j54n1n/usbprog/board/selfmade_v3/ReadMe.txt

...noch ein Layout...

Moin!

Anbei ein weiteres Layout zum selber Ätzen. Dabei wurde der Schaltplan 
des originalen USBprog (Version 3.1) 1:1 übernommen und lediglich 
wenige Bauteilgrößen aus Routinggründen geändert. Das Layout ist 
komplett einseitig mit nur fünf Lötbrücken. Drei der Lötbrücken können 
theoretisch durch 0Ohm-Widerstände mit 1206er Baugröße ersetzt werden.
Hierauf habe ich allerdings verzichtet, da es sich bei den Brücken um 
die Versorgungsspannung handelt.
Die Abmessung der Platine ist mit 80mm x 37mm handlich geblieben.

Die abgeänderten Bauteilgrößen sind:
Name        Wert     Änderung
-----------+--------+-------------------------------
J1          -        Mini-USB-B statt Standard-USB-B
LED1,LED2   rt, gn   3mm-DIL statt 0603SMD
R8-15       100      1206 statt 0603
R7          10k      1206 statt 0603

Viel Spass beim Nachbauen!

MfG,
Thomas
<etechnik@gmx.info>
