j54n1n/usbprog/usbprogLCD/lcdhype/readme.txt

LCDHype Treiber für usbprog_lcd
===============================
(getestet mit LCDHype 0.42)

1. Treiber installieren
=======================
Komplettes Verzeichnis "usbprog" (inkl. Verzeichnisname) kopieren nach
C:\Programme\LCDHype\controller
In LCDHype unter Einstellungen => LCD-Einstellungen auswählen:
USBprog

2. Plugin für WinAmp installieren
=================================
Plugin für WinAmp (V2.xx) installieren (getestet mit WinAmp 2.73)
Alle Dateien aus dem Verzeichnis "winamp" kopieren nach
C:\Programme\Winamp\Plugins

3. Beispielskript
=================
Beispielskript zur Ausgabe von Titel/Interpret und Spektrumanalyzer aus WinAmp:
Datei "usblcd.sd" kopieren nach
C:\Programme\LCDHype\scripts
In LCDHype unter LCD-Anzeige dieses Skript laden und mit dem Go-Button starten.
