j54n1n/usbprog/board/hvpp.png

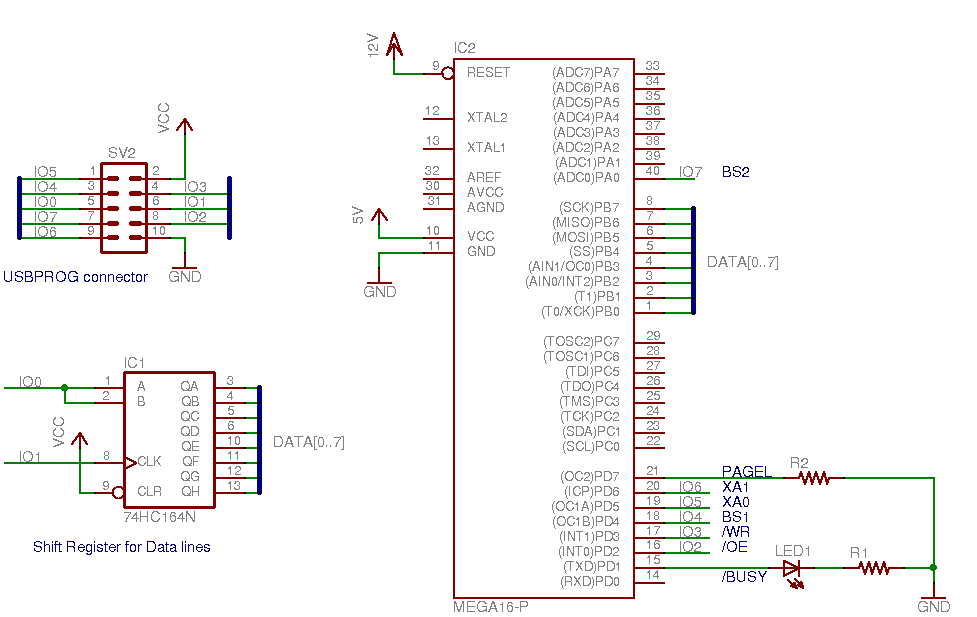
board/hvpp.png
