j54n1n/usbprog/board/levelshifter/screenshot.png

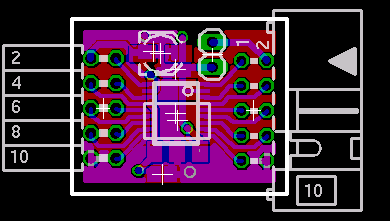
board/levelshifter/screenshot.png
