j54n1n/usbprog/board/selfmade_v3/bottom.jpg

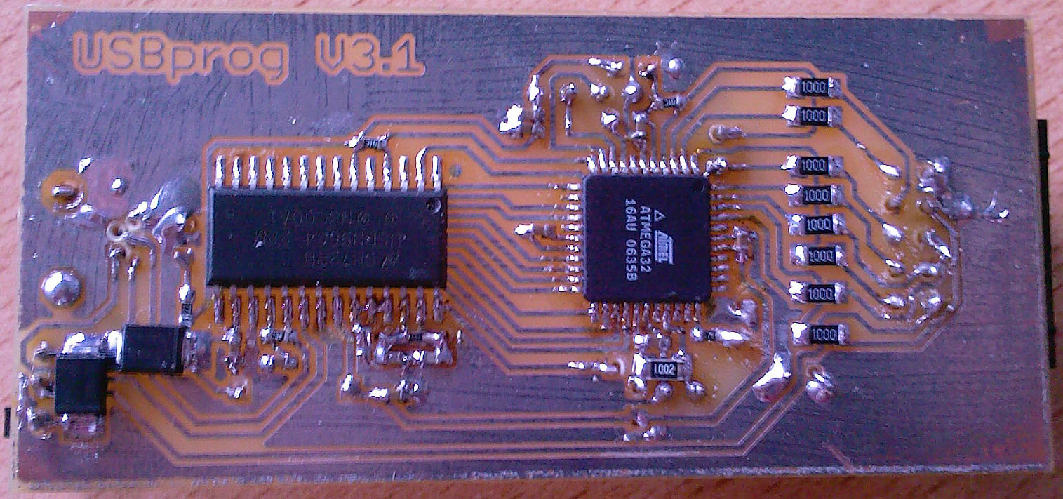
board/selfmade_v3/bottom.jpg
