j54n1n/usbprog/board/selfmade_v3/top.jpg

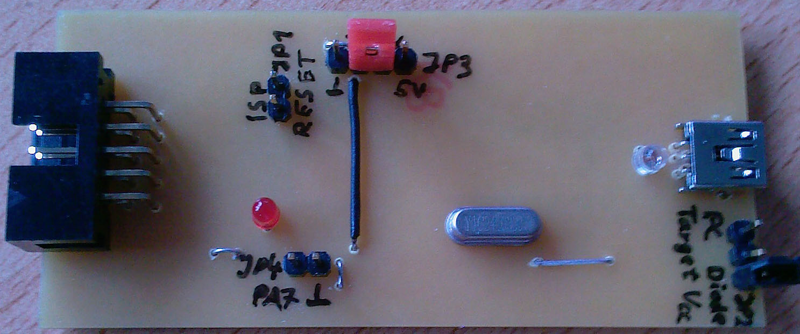
board/selfmade_v3/top.jpg
