j54n1n/usbprog/misc/selfmade_usbprog/BC5G3316.jpg

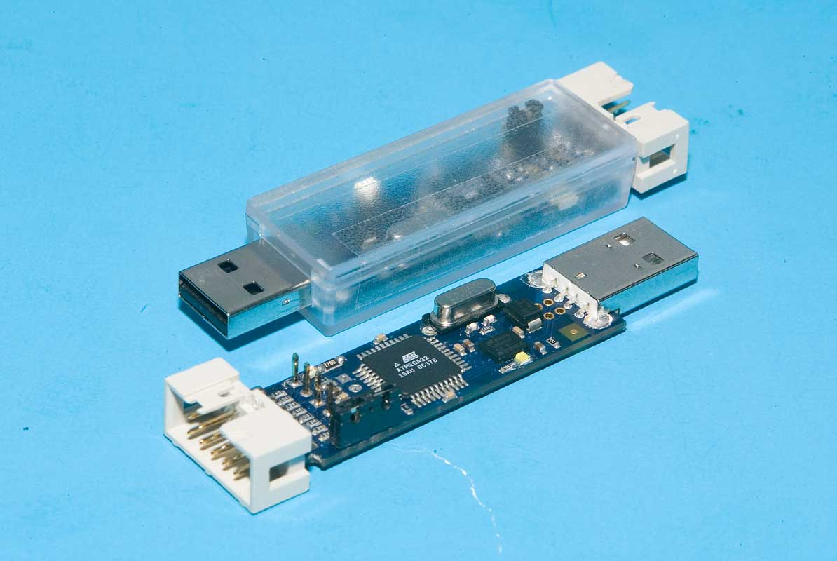
misc/selfmade_usbprog/BC5G3316.jpg
