j54n1n/usbprog/misc/selfmade_usbprog/P1010025.JPG

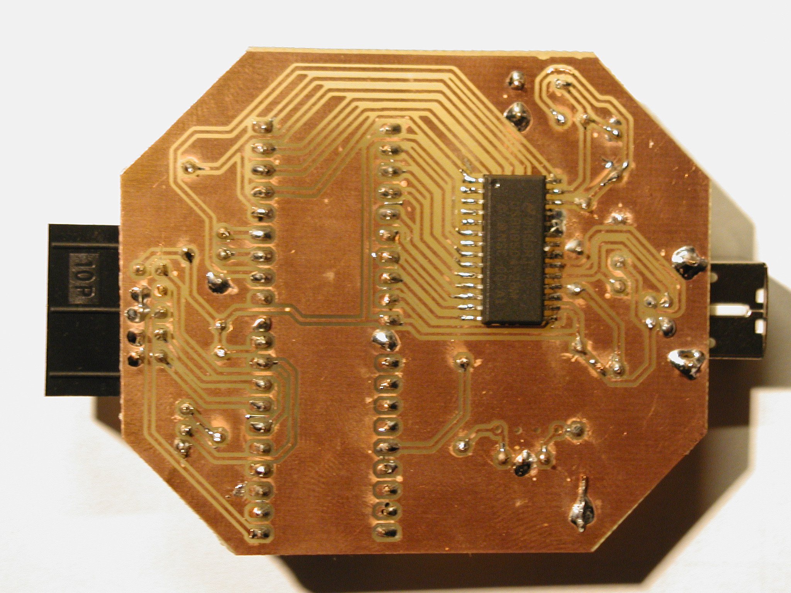
misc/selfmade_usbprog/P1010025.JPG
