j54n1n/usbprog/misc/selfmade_usbprog/P1010026.JPG

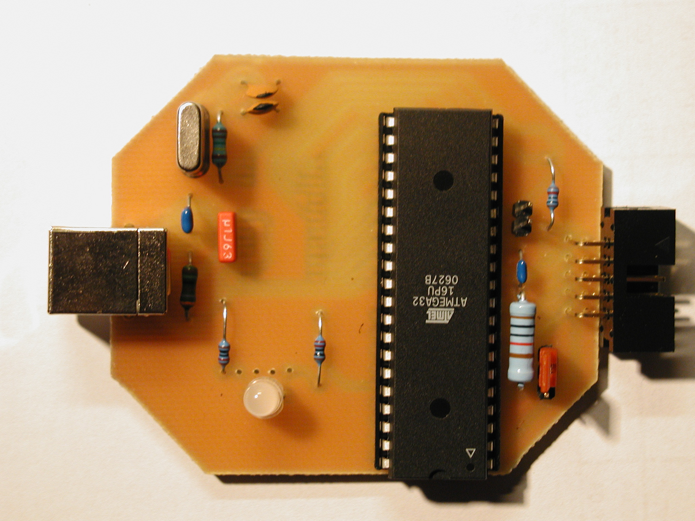
misc/selfmade_usbprog/P1010026.JPG
