j54n1n/usbprog/misc/selfmade_usbprog/UsbProgSharp-copper.jpg

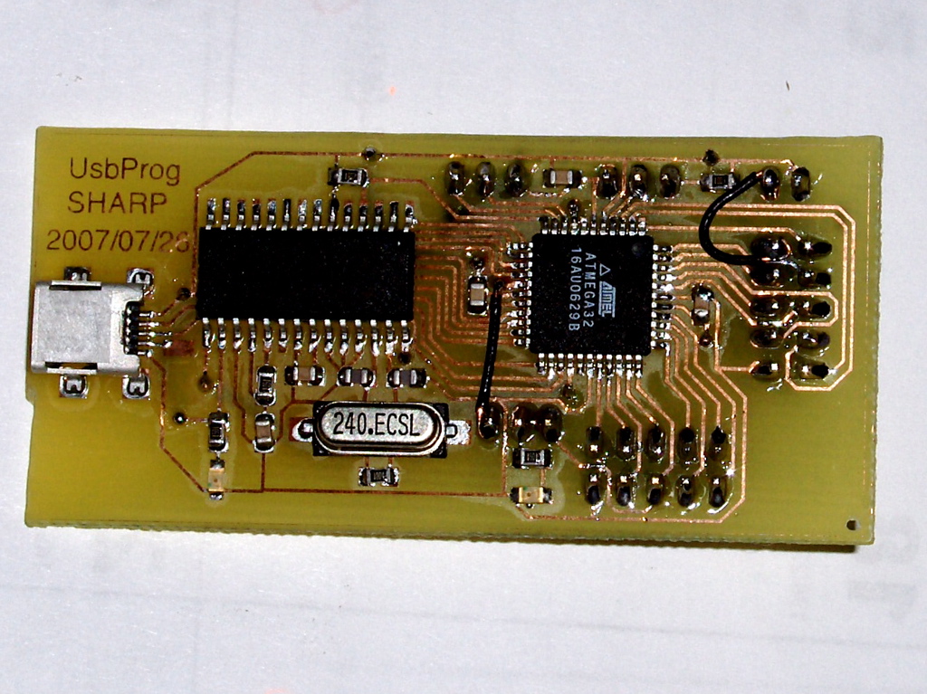
misc/selfmade_usbprog/UsbProgSharp-copper.jpg
