j54n1n/usbprog/usbprogCAN/board/usbprogCAN.png

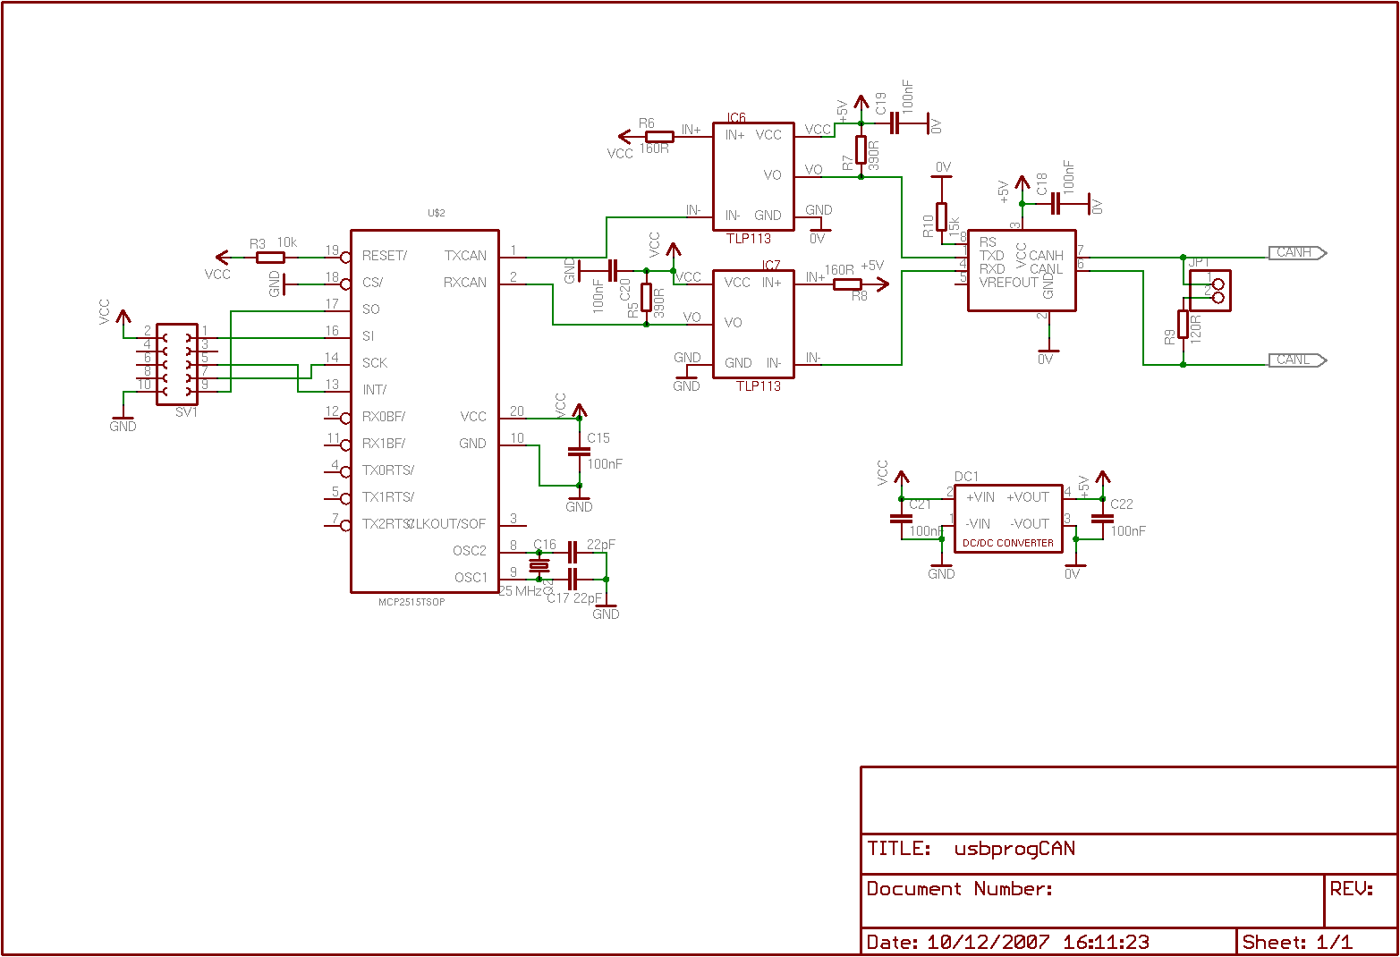
usbprogCAN/board/usbprogCAN.png
