j54n1n/usbprog/usbprogJTAG/openwince/website/iPAQ-3600/images/4.jpg

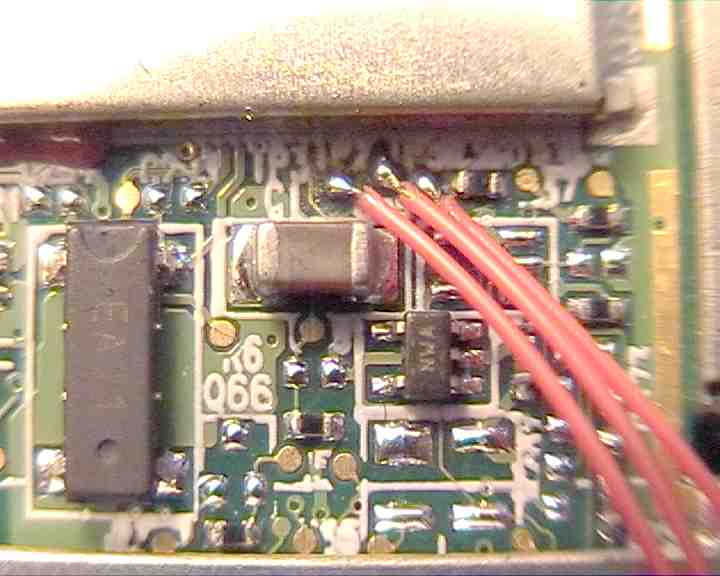
usbprogJTAG/openwince/website/iPAQ-3600/images/4.jpg
