j54n1n/usbprog/usbprogJTAG/openwince/website/iPAQ-3600/images/7.jpg

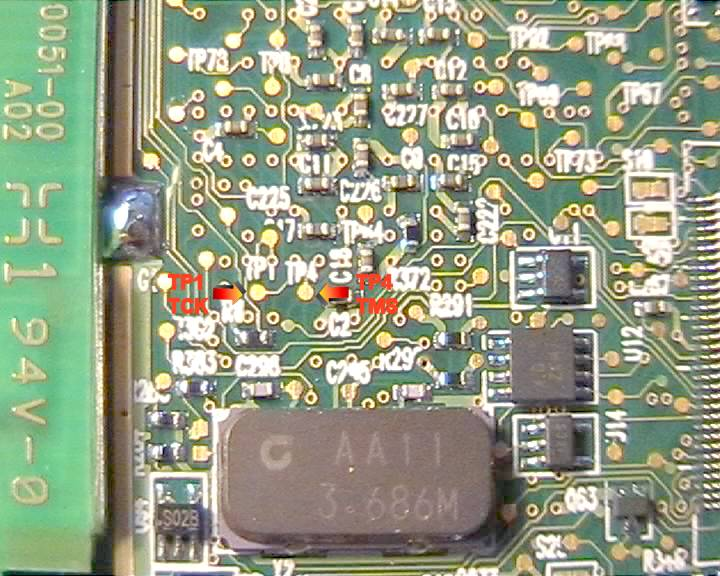
usbprogJTAG/openwince/website/iPAQ-3600/images/7.jpg
