j54n1n/usbprog/usbprogJTAG/openwince/website/iPAQ-3600/images/12.jpg

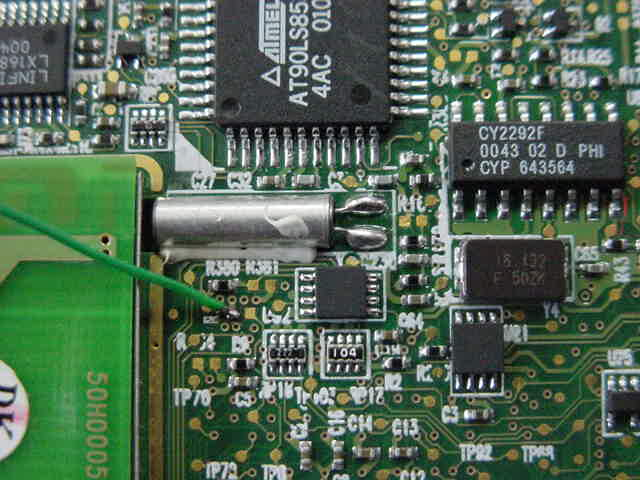
usbprogJTAG/openwince/website/iPAQ-3600/images/12.jpg
