j54n1n/usbprog/usbprogJTAG/openwince/website/iPAQ-3600/images/A.jpg

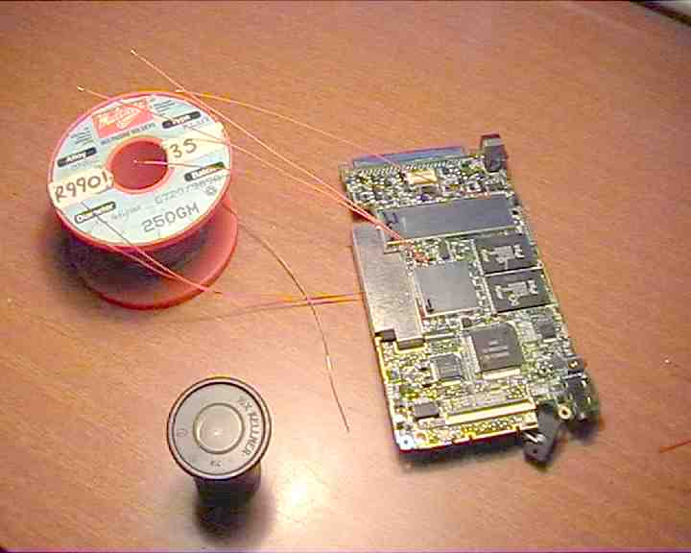
usbprogJTAG/openwince/website/iPAQ-3600/images/A.jpg
