j54n1n/usbprog/usbprogJTAG/openwince/website/iPAQ-3600/images/B.jpg

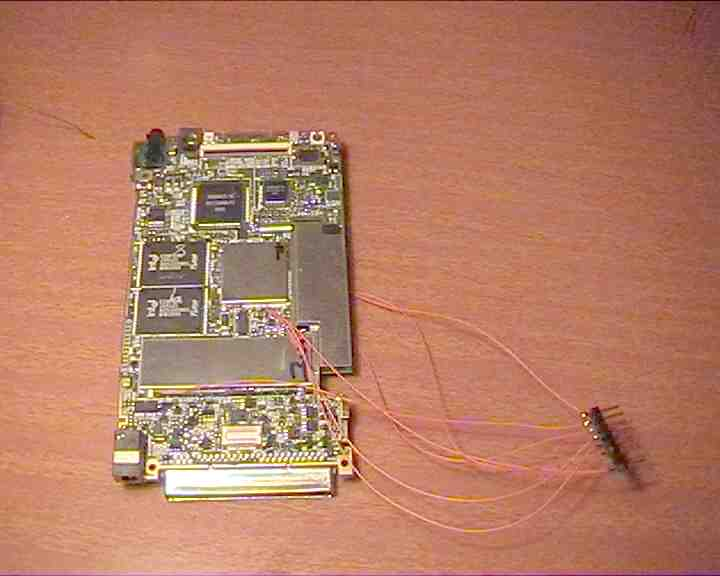
usbprogJTAG/openwince/website/iPAQ-3600/images/B.jpg
