j54n1n/usbprog/usbprogLCD/images/lcd.jpg

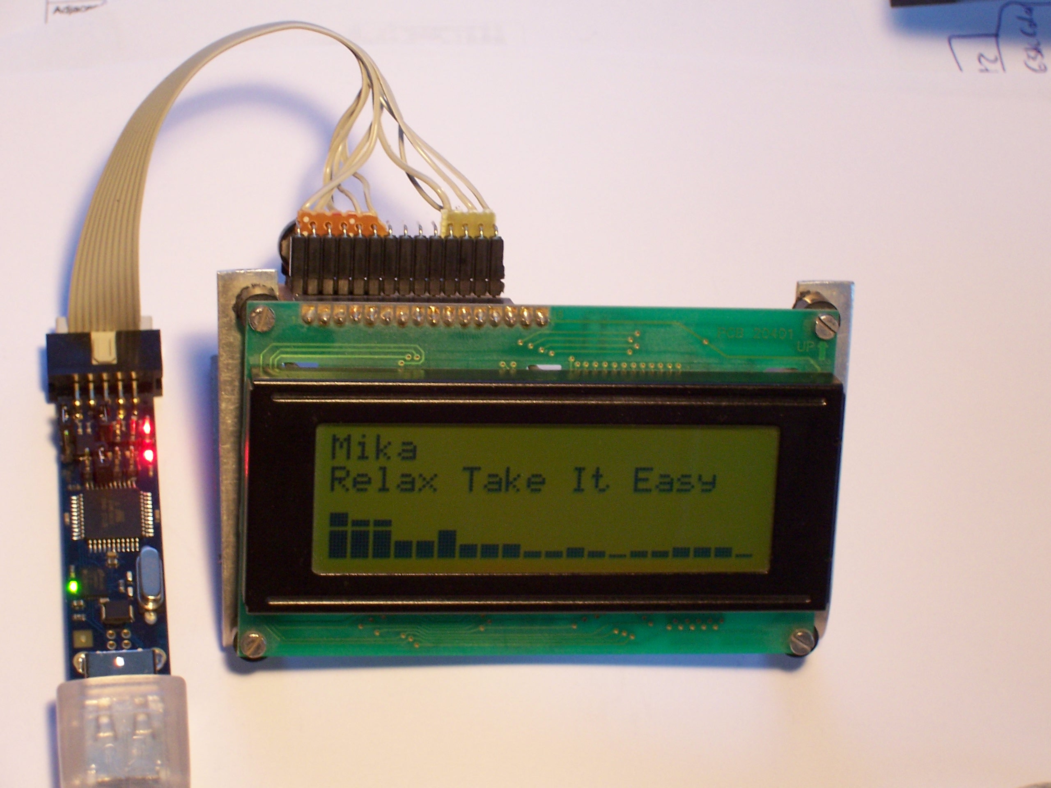
usbprogLCD/images/lcd.jpg
