j54n1n/usbprog/usbprogPIC/levelshifter/circuit.png

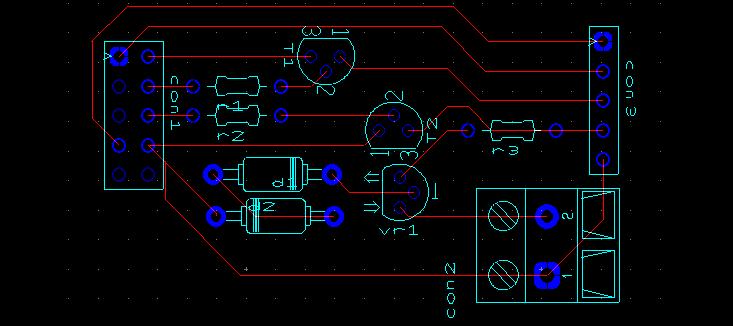
usbprogPIC/levelshifter/circuit.png
