j54n1n/usbprog/usbprogJTAG/openwince-include-0.4.2/arm/pxa2x0/gpio.h

/*
 * $Id: gpio.h,v 1.14 2005/09/29 08:51:07 telka Exp $
 *
 * XScale PXA26x/PXA255/PXA250/PXA210 GPIO Registers
 * Copyright (C) 2002, 2003 ETC s.r.o.
 * All rights reserved.
 *
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
 * Written by Marcel Telka <marcel@telka.sk>, 2002, 2003.
 *
 * Documentation:
 * [1] Intel Corporation, "Intel PXA250 and PXA210 Application Processors
 *     Developer's Manual", February 2002, Order Number: 278522-001
 * [2] Intel Corporation, "Intel PXA26x Processor Family Developer's Manual",
 *     March 2003, Order Number: 278638-002
 * [3] Intel Corporation, "Intel PXA255 Processor Developer's Manual"
 *     March 2003, Order Number: 278693-001
 *
 */

#ifndef	PXA2X0_GPIO_H
#define	PXA2X0_GPIO_H

#include <openwince.h>

#if LANGUAGE == C
#include <stdint.h>
#endif

#if defined(PXA2X0_NOPXA250) && !defined(PXA2X0_NOPXA255)
#define PXA2X0_NOPXA255
#endif

#if defined(PXA2X0_NOPXA255) && !defined(PXA2X0_NOPXA260)
#define PXA2X0_NOPXA260
#endif

/* GPIO Registers */

#define	GPIO_BASE	0x40E00000

#if LANGUAGE == C
typedef volatile struct GPIO_registers {
	uint32_t gplr0;
	uint32_t gplr1;
	uint32_t gplr2;
	uint32_t gpdr0;
	uint32_t gpdr1;
	uint32_t gpdr2;
	uint32_t gpsr0;
	uint32_t gpsr1;
	uint32_t gpsr2;
	uint32_t gpcr0;
	uint32_t gpcr1;
	uint32_t gpcr2;
	uint32_t grer0;
	uint32_t grer1;
	uint32_t grer2;
	uint32_t gfer0;
	uint32_t gfer1;
	uint32_t gfer2;
	uint32_t gedr0;
	uint32_t gedr1;
	uint32_t gedr2;
	uint32_t gafr0_l;
	uint32_t gafr0_u;
	uint32_t gafr1_l;
	uint32_t gafr1_u;
	uint32_t gafr2_l;
	uint32_t gafr2_u;
} GPIO_registers_t;

#ifdef PXA2X0_UNMAPPED
#define	GPIO_pointer	((GPIO_registers_t*) GPIO_BASE)
#endif

#define	GPLR0		GPIO_pointer->gplr0
#define	GPLR1		GPIO_pointer->gplr1
#define	GPLR2		GPIO_pointer->gplr2
#define	GPDR0		GPIO_pointer->gpdr0
#define	GPDR1		GPIO_pointer->gpdr1
#define	GPDR2		GPIO_pointer->gpdr2
#define	GPSR0		GPIO_pointer->gpsr0
#define	GPSR1		GPIO_pointer->gpsr1
#define	GPSR2		GPIO_pointer->gpsr2
#define	GPCR0		GPIO_pointer->gpcr0
#define	GPCR1		GPIO_pointer->gpcr1
#define	GPCR2		GPIO_pointer->gpcr2
#define	GRER0		GPIO_pointer->grer0
#define	GRER1		GPIO_pointer->grer1
#define	GRER2		GPIO_pointer->grer2
#define	GFER0		GPIO_pointer->gfer0
#define	GFER1		GPIO_pointer->gfer1
#define	GFER2		GPIO_pointer->gfer2
#define	GEDR0		GPIO_pointer->gedr0
#define	GEDR1		GPIO_pointer->gedr1
#define	GEDR2		GPIO_pointer->gedr2
#define	GAFR0_L		GPIO_pointer->gafr0_l
#define	GAFR0_U		GPIO_pointer->gafr0_u
#define	GAFR1_L		GPIO_pointer->gafr1_l
#define	GAFR1_U		GPIO_pointer->gafr1_u
#define	GAFR2_L		GPIO_pointer->gafr2_l
#define	GAFR2_U		GPIO_pointer->gafr2_u
#endif /* LANGUAGE == C */

#define	GPLR0_OFFSET	0x00
#define	GPLR1_OFFSET	0x04
#define	GPLR2_OFFSET	0x08
#define	GPDR0_OFFSET	0x0C
#define	GPDR1_OFFSET	0x10
#define	GPDR2_OFFSET	0x14
#define	GPSR0_OFFSET	0x18
#define	GPSR1_OFFSET	0x1C
#define	GPSR2_OFFSET	0x20
#define	GPCR0_OFFSET	0x24
#define	GPCR1_OFFSET	0x28
#define	GPCR2_OFFSET	0x2C
#define	GRER0_OFFSET	0x30
#define	GRER1_OFFSET	0x34
#define	GRER2_OFFSET	0x38
#define	GFER0_OFFSET	0x3C
#define	GFER1_OFFSET	0x40
#define	GFER2_OFFSET	0x44
#define	GEDR0_OFFSET	0x48
#define	GEDR1_OFFSET	0x4C
#define	GEDR2_OFFSET	0x50
#define	GAFR0_L_OFFSET	0x54
#define	GAFR0_U_OFFSET	0x58
#define	GAFR1_L_OFFSET	0x5C
#define	GAFR1_U_OFFSET	0x60
#define	GAFR2_L_OFFSET	0x64
#define	GAFR2_U_OFFSET	0x68

/* GPIO bits - see Table 2-11 in [1] */

#define	GPIO0_GP0	bit(0)
#define	GPIO0_GP1	bit(1)
#if !defined(PXA2X0_NOPXA250)
#define	GPIO0_GP2	bit(2)
#define	GPIO0_GP3	bit(3)
#define	GPIO0_GP4	bit(4)
#define	GPIO0_GP5	bit(5)
#define	GPIO0_GP6	bit(6)
#define	GPIO0_GP7	bit(7)
#define	GPIO0_GP8	bit(8)
#define	GPIO0_GP9	bit(9)
#define	GPIO0_GP10	bit(10)
#define	GPIO0_GP11	bit(11)
#define	GPIO0_GP12	bit(12)
#define	GPIO0_GP13	bit(13)
#define	GPIO0_GP14	bit(14)
#endif /* PXA250 and above only */
#define	GPIO0_GP15	bit(15)
#define	GPIO0_GP16	bit(16)
#define	GPIO0_GP17	bit(17)
#define	GPIO0_GP18	bit(18)
#if !defined(PXA2X0_NOPXA250)
#define	GPIO0_GP19	bit(19)
#define	GPIO0_GP20	bit(20)
#define	GPIO0_GP21	bit(21)
#define	GPIO0_GP22	bit(22)
#endif /* PXA250 and above only */
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
#define	GAFR2_L_AF76(x)	(((x) & ALT_FN_MASK) << 24)
#define	GAFR2_L_AF77(x)	(((x) & ALT_FN_MASK) << 26)
#define	GAFR2_L_AF78(x)	(((x) & ALT_FN_MASK) << 28)
#define	GAFR2_L_AF79(x)	(((x) & ALT_FN_MASK) << 30)

/* GAFR2_U bits - see Table 4-29 in [1], Table 4-29 in [2], Table 4-29 in [3] */

#define	GAFR2_U_AF80(x)	((x) & ALT_FN_MASK)
#if !defined(PXA2X0_NOPXA255)
#define	GAFR2_U_AF81(x)	(((x) & ALT_FN_MASK) << 2)
#define	GAFR2_U_AF82(x)	(((x) & ALT_FN_MASK) << 4)
#define	GAFR2_U_AF83(x)	(((x) & ALT_FN_MASK) << 6)
#define	GAFR2_U_AF84(x)	(((x) & ALT_FN_MASK) << 8)
#endif /* PXA255 and above only */
#if !defined(PXA2X0_NOPXA260)
#define	GAFR2_U_AF85(x)	(((x) & ALT_FN_MASK) << 10)
#define	GAFR2_U_AF86(x)	(((x) & ALT_FN_MASK) << 12)
#define	GAFR2_U_AF87(x)	(((x) & ALT_FN_MASK) << 14)
#define	GAFR2_U_AF88(x)	(((x) & ALT_FN_MASK) << 16)
#define	GAFR2_U_AF89(x)	(((x) & ALT_FN_MASK) << 18)
#endif /* PXA260 and above only */

#endif /* PXA2X0_GPIO_H */
