j54n1n/usbprog/misc/avarice_corner/avarice/src/main.cc

/*
 *	avarice - The "avarice" program.
 *	Copyright (C) 2001 Scott Finneran
 *	Copyright (C) 2002, 2003, 2004 Intel Corporation
 *	Copyright (C) 2005,2006 Joerg Wunsch
 *
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
 *
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
 * This file contains the main() & support for avrjtagd.
 *
 * $Id: main.cc,v 1.38 2006/10/28 20:17:31 joerg_wunsch Exp $
 */


#include <ctype.h>
#include <stdio.h>
#include <stdlib.h>
#include <string.h>
#include <sys/types.h>
#include <sys/socket.h>
#include <termios.h>
#include <arpa/inet.h>
#include <netdb.h>
#include <netinet/in.h>
#include <unistd.h>
#include <netinet/tcp.h>
#include <fcntl.h>

#include "avarice.h"
#include "remote.h"
#include "jtag.h"
#include "jtag1.h"
#include "jtag2.h"
#include "gnu_getopt.h"

bool ignoreInterrupts;

static int makeSocket(struct sockaddr_in *name, unsigned short int port)
{
    int sock;
    int tmp;
    struct protoent *protoent;

    sock = socket(PF_INET, SOCK_STREAM, 0);
    gdbCheck(sock);

    // Allow rapid reuse of this port.
    tmp = 1;
    gdbCheck(setsockopt(sock, SOL_SOCKET, SO_REUSEADDR, (char *)&tmp, sizeof(tmp)));

    // Enable TCP keep alive process.
    tmp = 1;
    gdbCheck(setsockopt(sock, SOL_SOCKET, SO_KEEPALIVE, (char *)&tmp, sizeof(tmp)));

    gdbCheck(bind(sock, (struct sockaddr *)name, sizeof(*name)));

    protoent = getprotobyname("tcp");
    check(protoent != NULL, "tcp protocol unknown (oops?)");

    tmp = 1;
    gdbCheck(setsockopt(sock, protoent->p_proto, TCP_NODELAY,
			(char *)&tmp, sizeof(tmp)));

    return sock;
}


static void initSocketAddress(struct sockaddr_in *name,
			      const char *hostname, unsigned short int port)
{
    struct hostent *hostInfo;

    memset(name, 0, sizeof(*name));
    name->sin_family = AF_INET;
    name->sin_port = htons(port);
    // Try numeric interpretation (1.2.3.4) first, then
    // hostname resolution if that failed.
    if (inet_aton(hostname, &name->sin_addr) == 0)
    {
	hostInfo = gethostbyname(hostname);
	check(hostInfo != NULL, "Unknown host %s", hostname);
	name->sin_addr = *(struct in_addr *)hostInfo->h_addr;
    }
}

static unsigned long parseJtagBitrate(const char *val)
{
    char *endptr, c;
    unsigned long v;

    check(*val != '\0', "invalid number in JTAG bit rate");
    v = strtoul(val, &endptr, 10);
    if (*endptr == '\0')
	return v;
    while (isspace((unsigned char)(c = *endptr)))
	endptr++;
    switch (c)
    {
    case 'k':
    case 'K':
	v *= 1000UL;
	return v;
    case 'm':
    case 'M':
	v *= 1000000UL;
	return v;
    }
    if (strcmp(endptr, "Hz") == 0)
	return v;

    check(false, "invalid number in JTAG bit rate");
    return 0UL;
}

static void usage(const char *progname)
{
    fprintf(stderr,
	    "Usage: %s [OPTION]... [[HOST_NAME]:PORT]\n\n", progname);
    fprintf(stderr, "Options:\n");
    fprintf(stderr,
	    "  -h, --help                  Print this message.\n");
    fprintf(stderr,
	    "  -1, --mkI                   Connect to JTAG ICE mkI (default)\n");
    fprintf(stderr,
	    "  -2, --mkII                  Connect to JTAG ICE mkII\n");
    fprintf(stderr,
            "  -B, --jtag-bitrate <rate>   Set the bitrate that the JTAG box communicates\n"
            "                                with the avr target device. This must be less\n"
            "                                than 1/4 of the frequency of the target. Valid\n"
            "                                values are 1MHz, 500KHz, 250KHz or 125KHz.\n"
            "                                (default: 1MHz)\n");
    fprintf(stderr,
	    "  -C, --capture               Capture running program.\n"
	    "                                Note: debugging must have been enabled prior\n"
            "                                to starting the program. (e.g., by running\n"
            "                                avarice earlier)\n");
    fprintf(stderr,
	    "  -c, --daisy-chain <ub,ua,bb,ba> Daisy chain settings:\n"
	    "                                <units before, units after,\n"
	    "                                bits before, bits after>\n");
    fprintf(stderr,
	    "  -D, --detach                Detach once synced with JTAG ICE\n");
    fprintf(stderr,
	    "  -d, --debug                 Enable printing of debug information.\n");
    fprintf(stderr,
            "  -e, --erase                 Erase target.\n");
    fprintf(stderr,
	    "  -f, --file <filename>       Specify a file for use with the --program and\n"
            "                                --verify options. If --file is passed and\n"
            "                                neither --program or --verify are given then\n"
            "                                --program is implied.\n");
    fprintf(stderr,
	    "  -g, --dragon                Connect to an AVR Dragon rather than a JTAG ICE.\n"
	    "                                This implies --mkII, but might be required in\n"
	    "                                addition to --debugwire when debugWire is to\n"
	    "                                be used.\n");
    fprintf(stderr,
	    "  -I, --ignore-intr           Automatically step over interrupts.\n"
	    "                                Note: EXPERIMENTAL. Can not currently handle\n"
            "                                devices fused for compatibility.\n");
    fprintf(stderr,
	    "  -j, --jtag <devname>        Port attached to JTAG box (default: /dev/avrjtag).\n");
    fprintf(stderr,
            "  -L, --write-lockbits <ll>   Write lock bits.\n");
    fprintf(stderr,
            "  -l, --read-lockbits         Read lock bits.\n");
    fprintf(stderr,
            "  -P, --part <name>           Target device name (e.g."
            " atmega16)\n\n");
    fprintf(stderr,
	    "  -p, --program               Program the target.\n"
	    "                                Binary filename must be specified with --file\n"
	    "                                option.\n");
    fprintf(stderr,
            "  -r, --read-fuses            Read fuses bytes.\n");
    fprintf(stderr,
	    "  -V, --version               Print version information.\n");
    fprintf(stderr,
            "  -v, --verify                Verify program in device against file specified\n"
            "                                with --file option.\n");
    fprintf(stderr,
	    "  -w, --debugwire             For the JTAG ICE mkII, connect to the target\n"
	    "                                using debugWire protocol rather than JTAG.\n");
    fprintf(stderr,
            "  -W, --write-fuses <eehhll>  Write fuses bytes.\n");
    fprintf(stderr,
	    "HOST_NAME defaults to 0.0.0.0 (listen on any interface).\n"
	    "\":PORT\" is required to put avarice into gdb server mode.\n\n");
    fprintf(stderr,
	    "e.g. %s --erase --program --file test.bin --jtag /dev/ttyS0 :4242\n\n",
	    progname);
    exit(1);
}

static struct option long_opts[] = {
    /* name,                 has_arg, flag,   val */
    { "mkI",                 0,       0,     '1' },
    { "mkII",                0,       0,     '2' },
    { "jtag-bitrate",        1,       0,     'B' },
    { "capture",             0,       0,     'C' },
    { "daisy-chain",         1,       0,     'c' },
    { "detach",              0,       0,     'D' },
    { "debug",               0,       0,     'd' },
    { "erase",               0,       0,     'e' },
    { "file",                1,       0,     'f' },
    { "dragon",              0,       0,     'g' },
    { "help",                0,       0,     'h' },
    { "ignore-intr",         0,       0,     'I' },
    { "jtag",                1,       0,     'j' },
    { "write-lockbits",      1,       0,     'L' },
    { "read-lockbits",       0,       0,     'l' },
    { "part",                1,       0,     'P' },
    { "program",             0,       0,     'p' },
    { "read-fuses",          0,       0,     'r' },
    { "version",             0,       0,     'V' },
    { "verify",              0,       0,     'v' },
    { "debugwire",           0,       0,     'w' },
    { "write-fuses",         1,       0,     'W' },
    { 0,                     0,       0,      0 }
};

jtag *theJtagICE;

int main(int argc, char **argv)
{
    int sock;
    struct sockaddr_in clientname;
    struct sockaddr_in name;
    char *inFileName = 0;
    char *jtagDeviceName = NULL;
    char *device_name = 0;
    unsigned long jtagBitrate = 0;
    const char *hostName = "0.0.0.0";	/* INADDR_ANY */
    int  hostPortNumber;
    bool erase = false;
    bool program = false;
    bool readFuses = false;
    bool writeFuses = false;
    char *fuses;
    bool readLockBits = false;
    bool writeLockBits = false;
    bool gdbServerMode = false;
    char *lockBits;
    bool detach = false;
    bool capture = false;
    bool verify = false;
    bool is_dragon = false;
    char *progname = argv[0];
    enum {
	MKI, MKII, MKII_DW
    } protocol = MKI;		// default to mkI protocol
    int  option_index;
    unsigned int units_before = 0;
    unsigned int units_after = 0;
    unsigned int bits_before = 0;
    unsigned int bits_after = 0;

    statusOut("AVaRICE version %s, %s %s\n\n",
	      PACKAGE_VERSION, __DATE__, __TIME__);

    device_name = 0;

    opterr = 0;                 /* disable default error message */

    while (1)
    {
        int c = getopt_long (argc, argv, "12B:Cc:Ddef:ghIj:L:lP:prVvwW:",
                             long_opts, &option_index);
        if (c == -1)
            break;              /* no more options */

        switch (c) {
            case 'h':
            case '?':
                usage(progname);
	    case '1':
		protocol = MKI;
		break;
	    case '2':
		// If we've already seen a -w option, don't revert to -2.
		if (protocol != MKII_DW)
		    protocol = MKII;
		break;
            case 'B':
		jtagBitrate = parseJtagBitrate(optarg);
                break;
            case 'C':
                capture = true;
                break;
            case 'c':
                if (sscanf(optarg,"%u,%u,%u,%u",
                           &units_before, &units_after,
                           &bits_before, &bits_after) != 4)
                    usage(progname);
		if (units_before > 255 || units_after > 255 ||
		    bits_before > 7 || bits_after > 7) {
		    fprintf(stderr,
			    "%s: daisy-chain parameters out of range\n",
			    progname);
		    exit(1);
		}
                break;
            case 'D':
                detach = true;
                break;
            case 'd':
                debugMode = true;
                break;
            case 'e':
                erase = true;
                break;
            case 'f':
                inFileName = optarg;
                break;
	    case 'g':
		// If we've already seen a -w option, don't revert to -2.
		if (protocol != MKII_DW)
		    protocol = MKII;
	        is_dragon = true;
		break;
            case 'I':
                ignoreInterrupts = true;
                break;
            case 'j':
                jtagDeviceName = optarg;
                break;
            case 'L':
                lockBits = optarg;
                writeLockBits = true;
                break;
            case 'l':
                readLockBits = true;
                break;
            case 'P':
                device_name = optarg;
                break;
            case 'p':
                program = true;
                break;
            case 'r':
                readFuses = true;
                break;
            case 'V':
                exit(0);
            case 'v':
                verify = true;
                break;
            case 'w':
	        protocol = MKII_DW;
		break;
            case 'W':
                fuses = optarg;
                writeFuses = true;
                break;
            default:
                fprintf (stderr, "getop() did something screwey");
                exit (1);
        }
    }

    if ((optind+1) == argc) {
        /* Looks like user has given [[host]:port], so parse out the host and
           port number then enable gdb server mode. */

        int i;
        char *arg = argv[optind];
        int len = strlen (arg);
        char *host = new char[len+1];
        memset (host, '\0', len+1);

        for (i=0; i<len; i++) {
            if ((arg[i] == '\0') || (arg[i] == ':'))
                break;

            host[i] = arg[i];
        }

        if (strlen (host)) {
            hostName = host;
        }

        if (arg[i] == ':') {
            i++;
        }

        if (i >= len) {
            /* No port was given. */
            fprintf (stderr, "avarice: %s is not a valid host:port value.\n",
                     arg);
            exit (1);
        }

        char *endptr;
        hostPortNumber = (int)strtol(arg+i, &endptr, 0);
        if (endptr == arg+i) {
            /* Invalid convertion. */
            fprintf (stderr, "avarice: failed to convert port number: %s\n",
                     arg+i);
            exit (1);
        }

        /* Make sure the the port value is not a priviledged port and is not
           greater than max port value. */

        if ((hostPortNumber < 1024) || (hostPortNumber > 0xffff)) {
            fprintf (stderr, "avarice: invalid port number: %d (must be >= %d"
                     " and <= %d)\n", hostPortNumber, 1024, 0xffff);
            exit (1);
        }

        gdbServerMode = true;
    }
    else if (optind != argc) {
        usage (progname);
    }

    if (jtagBitrate == 0)
    {
        fprintf (stdout,
                 "Defaulting JTAG bitrate to 1 MHz. Make sure that the target\n"
                 "frequency is at least 4 MHz or you will likely encounter failures\n"
                 "controlling the target.\n\n");

        jtagBitrate = 1000000;
    }

    // Use a default device name to connect to if not specified on the
    // command-line.  As the AVR Dragon can only be talked to through
    // USB, default it to USB, but use a generic name else.
    if (jtagDeviceName == NULL)
    {
      if (is_dragon)
	jtagDeviceName = "usb";
      else
	jtagDeviceName = "/dev/avrjtag";
    }

    try {
	// And say hello to the JTAG box
	switch (protocol) {
	case MKI:
	    theJtagICE = new jtag1(jtagDeviceName, device_name);
	    break;

	case MKII:
	    theJtagICE = new jtag2(jtagDeviceName, device_name, false, is_dragon);
	    break;

	case MKII_DW:
	    theJtagICE = new jtag2(jtagDeviceName, device_name, true, is_dragon);
	    break;
	}

	// Set Daisy-chain variables
	theJtagICE->dchain.units_before = (unsigned char) units_before;
	theJtagICE->dchain.units_after = (unsigned char) units_after;
	theJtagICE->dchain.bits_before = (unsigned char) bits_before;
	theJtagICE->dchain.bits_after = (unsigned char) bits_after;

	// Init JTAG box.
	theJtagICE->initJtagBox();
    }
    catch(const char *msg)
      {
	fprintf(stderr, "%s\n", msg);
	return 1;
      }
    catch(...)
      {
	fprintf(stderr, "Cannot initialize JTAG ICE\n");
	return 1;
      }

    if (erase)
    {
        theJtagICE->enableProgramming();
	statusOut("Erasing program memory.\n");
	theJtagICE->eraseProgramMemory();
	statusOut("Erase complete.\n");
        theJtagICE->disableProgramming();
    }

    if (readFuses)
    {
        theJtagICE->jtagReadFuses();
    }

    if (readLockBits)
    {
        theJtagICE->jtagReadLockBits();
    }

    if (writeFuses)
        theJtagICE->jtagWriteFuses(fuses);

    // Init JTAG debugger for initial use.
    //   - If we're attaching to a running target, we cannot do this.
    //   - If we're running as a standalone programmer, we don't want
    //     this.
    if( gdbServerMode && ( ! capture ) )
        theJtagICE->initJtagOnChipDebugging(jtagBitrate);

    if (inFileName != (char *)0)
    {
        if ((program == false) && (verify == false)) {
            /* If --file is given and neither --program or --verify, then we
               program, but not verify so as to be backward compatible with
               the old meaning of --file from before the addition of --program
               and --verify. */

            program = true;
        }

        if ((erase == false) && (program == true)) {
            statusOut("WARNING: The default behaviour has changed.\n"
                      "Programming no longer erases by default. If you want to"
                      " erase and program\nin a single step, use the --erase "
                      "in addition to --program. The reason for\nthis change "
                      "is to allow programming multiple sections (e.g. "
                      "application and\nbootloader) in multiple passes.\n\n");
        }

        theJtagICE->downloadToTarget(inFileName, program, verify);
        theJtagICE->resetProgram();
    }
    else
    {
	check( (!program) && (!verify),
	      "\nERROR: Filename not specified."
	      " Use the --file option.\n");
    }

    // Write fuses after all programming parts have completed.
    if (writeLockBits)
        theJtagICE->jtagWriteLockBits(lockBits);

    // Quit & resume mote for operations that don't interact with gdb.
    if (!gdbServerMode)
	theJtagICE->resumeProgram();
    else
    {
        initSocketAddress(&name, hostName, hostPortNumber);
        sock = makeSocket(&name, hostPortNumber);
        statusOut("Waiting for connection on port %hu.\n", hostPortNumber);
        gdbCheck(listen(sock, 1));

        if (detach)
        {
            int child = fork();

            unixCheck(child, "Failed to fork");
            if (child != 0)
                _exit(0);
            else
                unixCheck(setsid(), "setsid failed - weird bug");
        }

        // Connection request on original socket.
        socklen_t size = (socklen_t)sizeof(clientname);
        int gfd = accept(sock, (struct sockaddr *)&clientname, &size);
        gdbCheck(gfd);
        statusOut("Connection opened by host %s, port %hu.\n",
                  inet_ntoa(clientname.sin_addr), ntohs(clientname.sin_port));

        setGdbFile(gfd);

        // Now do the actual processing of GDB messages
        // We stay here until exiting because of error of EOF on the
        // gdb connection
        for (;;)
            talkToGdb();
    }

    delete theJtagICE;

    return 0;
}
