j54n1n/usbprog/openocd/firmware/usbprogjtag.c

/*
 * Copyright (C) 2006 Benedikt Sauter 
 *
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
 * You should have received a copy of the GNU General Public License
 * along with this program; if not, write to the Free Software
 * Foundation, Inc., 59 Temple Place, Suite 330, Boston, MA  02111-1307  USA
 */

#include "usbprogjtag.h"

void write_and_read(char * buf, uint16_t size)
{
  uint16_t i,j;
  // until byte 3 (0=cmd,1,2=size,3... data)
  uint16_t bit_cnt;
  for (bit_cnt = 0; bit_cnt < size; bit_cnt++) {
    // write tdi
    
    // control tdi
    if ((buf[(bit_cnt+24)/8] >> ((bit_cnt+24) % 8)) & 0x1) //tdi 1
      SETBIT(BIT3_WRITE,BIT3);
    else // tdi 0
      CLEARBIT(BIT3_WRITE,BIT3);
    
    // control tms line - goes to high at last bit
    if(size != 488){
      if(bit_cnt==(size-1))
	SETBIT(BIT1_WRITE,BIT1);
      else
	CLEARBIT(BIT1_WRITE,BIT1);
    }
    
    // clock
    CLEARBIT(BIT2_WRITE,BIT2);
    //asm("nop");
    //for(i=0;i<0xFF;i++)asm("nop");
    asm("nop");
    SETBIT(BIT2_WRITE,BIT2);

    // read tdo
    if(IS_BIT0_SET())
      buf[(bit_cnt+24)/8] |= 1 << ((bit_cnt+24) % 8);
    else
      buf[(bit_cnt+24)/8] &= ~(1 << ((bit_cnt+24) % 8));
  }
}


void write_tdi(char * buf, uint16_t size)
{

  uint16_t i,j;
  // until byte 3 (0=cmd,1,2=size,3... data)
  uint16_t bit_cnt;
  
  for (bit_cnt = 0; bit_cnt < size; bit_cnt++) {
    // write tdi
    
    // control tdi
    if ((buf[(bit_cnt+24)/8] >> ((bit_cnt+24) % 8)) & 0x1) //tdi 1
      SETBIT(BIT3_WRITE,BIT3);
    else // tdi 0
      CLEARBIT(BIT3_WRITE,BIT3);
    // control tms line - goes to high at last bit
    if(size != 488){
      if(bit_cnt==(size-1))
	SETBIT(BIT1_WRITE,BIT1);
      else
	CLEARBIT(BIT1_WRITE,BIT1);
    }
    // clock
    CLEARBIT(BIT2_WRITE,BIT2);
    asm("nop");
    //for(i=0;i<0xFF;i++)asm("nop");
    //asm("nop");
    SETBIT(BIT2_WRITE,BIT2);
  }
}

void write_tms(uint8_t buf)
{

  uint8_t i;
  CLEARBIT(BIT3_WRITE,BIT3);
  // until byte 3 (0=cmd,1,2=size,3... data)
  uint8_t tms; 
  for (i = 0; i < 7; i++) {
    // write tdi
    
    // control tdi
    tms = ((buf >> i) & 1); //tdi 1
    if (tms) //tdi 1
      SETBIT(BIT1_WRITE,BIT1);
    else // tdi 0
      CLEARBIT(BIT1_WRITE,BIT1);
    
    // clock
    CLEARBIT(BIT2_WRITE,BIT2);
    asm("nop");
    asm("nop");
    asm("nop");
    asm("nop");
    SETBIT(BIT2_WRITE,BIT2);
  }
 
  // from openocd moved to here
  CLEARBIT(BIT2_WRITE,BIT2);
  if (tms) //tdi 1
    SETBIT(BIT1_WRITE,BIT1);
  else // tdi 0
    CLEARBIT(BIT1_WRITE,BIT1);

}

void read_tdo(char * buf, uint16_t size)
{
  uint16_t i,j;
  // until byte 3 (0=cmd,1,2=size,3... data)
  uint16_t bit_cnt;
  for (bit_cnt = 0; bit_cnt < size; bit_cnt++) {
    
    // control tms line - goes to high at last bit
    if(size != 488){
      if(bit_cnt==(size-1))
	SETBIT(BIT1_WRITE,BIT1);
      else
	CLEARBIT(BIT1_WRITE,BIT1);
    }
    
    // clock
    CLEARBIT(BIT2_WRITE,BIT2);
    asm("nop");
    //for(i=0;i<0xFF;i++)asm("nop");
    //asm("nop");
    SETBIT(BIT2_WRITE,BIT2);

    // read tdo
    if(IS_BIT0_SET())
      buf[(bit_cnt+24)/8] |= 1 << ((bit_cnt+24) % 8);
    else
      buf[(bit_cnt+24)/8] &= ~(1 << ((bit_cnt+24) % 8));
  }

}





void set_direction(uint8_t direction)
{
  // 0 = input, 1 = output
  if(direction & 0x01) SETBIT(BIT0_DDR,BIT0); else CLEARBIT(BIT0_DDR,BIT0);
  if(direction & 0x02) SETBIT(BIT1_DDR,BIT1); else CLEARBIT(BIT1_DDR,BIT1);
  if(direction & 0x04) SETBIT(BIT2_DDR,BIT2); else CLEARBIT(BIT2_DDR,BIT2);
  if(direction & 0x08) SETBIT(BIT3_DDR,BIT3); else CLEARBIT(BIT3_DDR,BIT3);
  if(direction & 0x10) SETBIT(BIT4_DDR,BIT4); else CLEARBIT(BIT4_DDR,BIT4);
  if(direction & 0x10) SETBIT(BIT4_1_DDR,BIT4_1); else CLEARBIT(BIT4_1_DDR,BIT4_1);
  if(direction & 0x20) SETBIT(BIT5_DDR,BIT5); else CLEARBIT(BIT5_DDR,BIT5);
  if(direction & 0x20) SETBIT(BIT5_1_DDR,BIT5_1); else CLEARBIT(BIT5_1_DDR,BIT5_1);
  if(direction & 0x40) SETBIT(BIT6_DDR,BIT6); else CLEARBIT(BIT6_DDR,BIT6);
}


void set_port(uint8_t value)
{
  // BIT0 - BIT 3
  //PORTB hinbauen	
/*
  uint8_t port=0;
  if(value & 0x01) port |= (1<<BIT0);
  if(value & 0x02) port |= (1<<BIT1);
  if(value & 0x04) port |= (1<<BIT2);
  if(value & 0x08) port |= (1<<BIT3);

  // all together
  //PORTB = port;
*/ 
  
  if(value & 0x01) SETBIT(BIT0_WRITE,BIT0); else CLEARBIT(BIT0_WRITE,BIT0);
  if(value & 0x02) SETBIT(BIT1_WRITE,BIT1); else CLEARBIT(BIT1_WRITE,BIT1);
  if(value & 0x04) SETBIT(BIT2_WRITE,BIT2); else CLEARBIT(BIT2_WRITE,BIT2);
  if(value & 0x08) SETBIT(BIT3_WRITE,BIT3); else CLEARBIT(BIT3_WRITE,BIT3);
  
/*
  //BIT4 - BIT 5
  if(value & 0x10) SETBIT(BIT4_WRITE,BIT4); else CLEARBIT(BIT4_WRITE,BIT4);
  if(value & 0x20) SETBIT(BIT5_WRITE,BIT5); else CLEARBIT(BIT5_WRITE,BIT5);

  // BIT 6
  if(value & 0x40) SETBIT(BIT6_WRITE,BIT6); else CLEARBIT(BIT6_WRITE,BIT6);
*/
}

uint8_t get_port()
{
  uint8_t result=0x00; 
  if(IS_BIT0_SET()) result |= (1<<BIT0);
  if(IS_BIT1_SET()) result |= (1<<BIT1);
  if(IS_BIT2_SET()) result |= (1<<BIT2);
  if(IS_BIT3_SET()) result |= (1<<BIT3);
  if(IS_BIT4_SET()) result |= (1<<BIT4);
  if(IS_BIT4_1_SET()) result |= (1<<BIT4);
  if(IS_BIT5_SET()) result |= (1<<BIT5);
  if(IS_BIT5_1_SET()) result |= (1<<BIT5);
  if(IS_BIT6_SET()) result |= (1<<BIT6);
  return result;
}


void set_bit(uint8_t bit, uint8_t value)
{
  switch(bit) {
    case 0: if(value==1) SETBIT(BIT0_WRITE,BIT0); else CLEARBIT(BIT0_WRITE,BIT0); break;
    case 1: if(value==1) SETBIT(BIT1_WRITE,BIT1); else CLEARBIT(BIT1_WRITE,BIT1); break;
    case 2: if(value==1) SETBIT(BIT2_WRITE,BIT2); else CLEARBIT(BIT2_WRITE,BIT2); break;
    case 3: if(value==1) SETBIT(BIT3_WRITE,BIT3); else CLEARBIT(BIT3_WRITE,BIT3); break;
    case 4: if(value==1) SETBIT(BIT4_WRITE,BIT4); else CLEARBIT(BIT4_WRITE,BIT4);
	    if(value==1) SETBIT(BIT4_1_WRITE,BIT4_1); else CLEARBIT(BIT4_1_WRITE,BIT4_1); break;
    case 5: if(value==1) SETBIT(BIT5_WRITE,BIT5); else CLEARBIT(BIT5_WRITE,BIT5);
	    if(value==1) SETBIT(BIT5_1_WRITE,BIT5_1); else CLEARBIT(BIT5_1_WRITE,BIT5_1); break;
    case 6: if(value==1) SETBIT(BIT5_WRITE,BIT6); else CLEARBIT(BIT6_WRITE,BIT6); break;
  }
}


uint8_t get_bit(uint8_t bit)
{
  switch(bit) {
    case 0: if(IS_BIT0_SET())return 1; else return 0; break;
    case 1: if(IS_BIT1_SET())return 1; else return 0; break;
    case 2: if(IS_BIT2_SET())return 1; else return 0; break;
    case 3: if(IS_BIT3_SET())return 1; else return 0; break;
    case 4: if(IS_BIT4_SET())return 1; else return 0; break;
    case 5: if(IS_BIT5_SET())return 1; else return 0; break;
    case 6: if(IS_BIT6_SET())return 1; else return 0; break;
  }
}
