j54n1n/usbprog/openocd/firmware/usbprogjtag.h

/*
 * Copyright (C) 2006 Benedikt Sauter 
 *
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
 * You should have received a copy of the GNU General Public License
 * along with this program; if not, write to the Free Software
 * Foundation, Inc., 59 Temple Place, Suite 330, Boston, MA  02111-1307  USA
 */
#include <stdint.h>
#include <avr/io.h>

#define BIT(x)            (1 << (x))
#define SETBIT(addr,x)    (addr |= BIT(x))
#define CLEARBIT(addr,x)  (addr &= ~BIT(x))

#define BIT0	    PB6
#define BIT1  	    PB0
#define BIT2	    PB7
#define BIT3	    PB5

#define BIT4	    PD0
#define BIT5	    PD1

#define BIT4_1	    PB3
#define BIT5_1	    PB4

#define BIT6	    PA4


#define BIT0_DDR    DDRB
#define BIT1_DDR    DDRB
#define BIT2_DDR    DDRB
#define BIT3_DDR    DDRB

#define BIT4_DDR    DDRD
#define BIT4_1_DDR    DDRB
#define BIT5_DDR    DDRD
#define BIT5_1_DDR    DDRB
#define BIT6_DDR    DDRA


#define BIT0_READ   PINB
#define BIT1_READ   PINB
#define BIT2_READ   PINB
#define BIT3_READ   PINB

#define BIT4_READ   PIND
#define BIT5_READ   PIND
#define BIT4_1_READ   PINB
#define BIT5_1_READ   PINB
#define BIT6_READ   PINA


#define BIT0_WRITE   PORTB
#define BIT1_WRITE   PORTB
#define BIT2_WRITE   PORTB
#define BIT3_WRITE   PORTB

#define BIT4_WRITE   PORTD
#define BIT5_WRITE   PORTD
#define BIT4_1_WRITE   PORTB
#define BIT5_1_WRITE   PORTB
#define BIT6_WRITE   PORTA

// check if tdo == 1
#define IS_BIT0_SET()			    (BIT0_READ & BIT(BIT0))
#define IS_BIT1_SET()			    (BIT1_READ & BIT(BIT1)) 
#define IS_BIT2_SET()			    (BIT2_READ & BIT(BIT2))
#define IS_BIT3_SET()			    (BIT3_READ & BIT(BIT3))

#define IS_BIT4_SET()			    (BIT4_READ & BIT(BIT4))
#define IS_BIT5_SET()			    (BIT5_READ & BIT(BIT5))
#define IS_BIT4_1_SET()			    (BIT4_1_READ & BIT(BIT4_1))
#define IS_BIT5_1_SET()			    (BIT5_1_READ & BIT(BIT5_1))
#define IS_BIT6_SET()			    (BIT6_READ & BIT(BIT6))


#define SET_BIT0()			     SETBIT( BIT0_WRITE, BIT0 )
#define SET_BIT1()			     SETBIT( BIT1_WRITE, BIT1 )
#define SET_BIT2()			     SETBIT( BIT2_WRITE, BIT2 )
#define SET_BIT3()			     SETBIT( BIT3_WRITE, BIT3 )

#define SET_BIT4()			     SETBIT( BIT4_WRITE, BIT4 )
#define SET_BIT5()			     SETBIT( BIT5_WRITE, BIT5 )
#define SET_BIT4_1()			     SETBIT( BIT4_1_WRITE, BIT4_1 )
#define SET_BIT5_1()			     SETBIT( BIT5_1_WRITE, BIT5_1 )
#define SET_BIT6()			     SETBIT( BIT6_WRITE, BIT6 )

#define CLEAR_BIT0()			     CLEARBIT( BIT0_WRITE, BIT0 )
#define CLEAR_BIT1()			     CLEARBIT( BIT1_WRITE, BIT1 )
#define CLEAR_BIT2()			     CLEARBIT( BIT2_WRITE, BIT2 )
#define CLEAR_BIT3()			     CLEARBIT( BIT3_WRITE, BIT3 )

#define CLEAR_BIT4()			     CLEARBIT( BIT4_WRITE, BIT4 )
#define CLEAR_BIT5()			     CLEARBIT( BIT5_WRITE, BIT5 )
#define CLEAR_BIT4_1()			     CLEARBIT( BIT4_1_WRITE, BIT4_1 )
#define CLEAR_BIT5_1()			     CLEARBIT( BIT5_1_WRITE, BIT5_1 )
#define CLEAR_BIT6()			     CLEARBIT( BIT6_WRITE, BIT6 )





void write_tdi(char * buf, uint16_t size);
void write_tms(uint8_t  buf);
void write_and_read(char * buf, uint16_t size);
void read_tdo(char * buf, uint16_t size);

void set_direction(uint8_t direction);
void set_port(uint8_t value);
uint8_t get_port();
void set_bit(uint8_t bit, uint8_t value);
uint8_t get_bit(uint8_t bit);
