j54n1n/usbprog/msp430/serJTAGfirmware/JTAGfunc.c

//part of mspgcc, modified file from TI:

/*==========================================================================*\
|                                                                            |
| JTAGfunc.c                                                                 |
|                                                                            |
| JTAG Control Sequences for Erasing / Programming / Fuse Burning            |
|----------------------------------------------------------------------------|
| Project:              JTAG Functions                                       |
| Developed using:      IAR Embedded Workbench 2.31C                         |
|----------------------------------------------------------------------------|
| Author:               FRGR                                                 |
| Version:              1.2                                                  |
| Initial Version:      04-17-02                                             |
| Last Change:          08-29-02                                             |
|----------------------------------------------------------------------------|
| Version history:                                                           |
| 1.0 04/02 FRGR        Initial version.                                     |
| 1.1 04/02 ALB2        Formatting changes, added comments.                  |
| 1.2 08/02 ALB2        Initial code release with Lit# SLAA149.              |
|----------------------------------------------------------------------------|
| Designed 2002 by Texas Instruments Germany                                 |
\*==========================================================================*/

#include "JTAGfunc.h"
#include "LowLevelFunc.h"

word DEVICE = 0;        // Global target device ID (e.g. 0xF149); is set 
                        // during GetDevice() function execution.

/****************************************************************************/
/* High level routines for accessing the target device via JTAG:            */
/*                                                                          */
/* From the following, the user is relieved from coding anything.           */
/* To provide better understanding and clearness, some functionality is     */
/* coded generously. (Code and speed optimization enhancements may          */
/* be desired)                                                              */
/****************************************************************************/

//----------------------------------------------------------------------------
/* This function sets the target JTAG state machine (JTAG FSM) back into the 
   Run-Test/Idle state after a shift access.
*/
void PrepTCLK(void)
{
  // JTAG FSM = Exit-DR
  ClrTCK();
  SetTCK();
  // JTAG FSM = Update-DR
  ClrTMS();
  ClrTCK();
  SetTCK();
  // JTAG FSM = Run-Test/Idle
}

//----------------------------------------------------------------------------
/* Function for shifting a given 16-bit word into the JTAG data register
   through TDI.
   Arguments: word data (16-bit data, MSB first)
   Result:    word (value is shifted out via TDO simultaneously)
*/
word DR_Shift16(word data)
{
  // JTAG FSM state = Run-Test/Idle
  SetTMS();
  ClrTCK();
  SetTCK();
  
  // JTAG FSM state = Select DR-Scan
  ClrTMS();
  ClrTCK();
  SetTCK();
  // JTAG FSM state = Capture-DR
  ClrTCK();
  SetTCK();
  
  // JTAG FSM state = Shift-DR, Shift in TDI (16-bit)
  return(Shift(F_WORD, data));
  // JTAG FSM state = Run-Test/Idle
}

//----------------------------------------------------------------------------
/* Function for shifting a new instruction into the JTAG instruction 
   register through TDI (MSB first, but with interchanged MSB - LSB, to
   simply use the same shifting function, Shift(), as used in DR_Shift16).
   Arguments: byte Instruction (8bit JTAG instruction, MSB first)
   Result:    word TDOword (value shifted out from TDO = JTAG ID)
*/
word IR_Shift(byte instruction)
{
  // JTAG FSM state = Run-Test/Idle
  SetTMS();
  ClrTCK();
  SetTCK();
  // JTAG FSM state = Select DR-Scan
  ClrTCK();
  SetTCK();
  
  // JTAG FSM state = Select IR-Scan
  ClrTMS();
  ClrTCK();
  SetTCK();
  // JTAG FSM state = Capture-IR
  ClrTCK();
  SetTCK();

  // JTAG FSM state = Shift-IR, Shift in TDI (8-bit)
  return(Shift(F_BYTE, instruction));
  // JTAG FSM state = Run-Test/Idle
}

//----------------------------------------------------------------------------
/* Reset target JTAG interface and perform fuse-HW check.
   Arguments: None
   Result:    None
*/
void ResetTAP(void)
{
  word i;
  
  SetTMS();
  SetTCK();
  // Perform fuse check
  ClrTMS();
  SetTMS();
  ClrTMS();
  SetTMS();
  // Now fuse is checked, Reset JTAG FSM
  for (i = 6; i > 0; i--)
  {
    ClrTCK();
    SetTCK();
  }
  // JTAG FSM is now in Test-Logic-Reset  
  ClrTCK();
  ClrTMS();
  SetTCK();
  // JTAG FSM is now in Run-Test/IDLE
}

//----------------------------------------------------------------------------
/* Function to execute a Power-Up Clear (PUC) using JTAG CNTRL SIG register
   Arguments: None
   Result:    word (STATUS_OK if JTAG ID is valid, STATUS_ERROR otherwise)
*/
word ExecutePUC(void)
{
        word JTAGVERSION;

        IR_Shift(IR_CNTRL_SIG_16BIT);
        DR_Shift16(0x2C01);               // Apply Reset
        DR_Shift16(0x2401);               // Remove Reset
        ClrTCLK();
        SetTCLK();
        ClrTCLK();
        SetTCLK();
        ClrTCLK();
        JTAGVERSION = IR_Shift(IR_ADDR_CAPTURE);
        SetTCLK();
        
        WriteMem(F_WORD, 0x0120, 0x5A80); // Disable Watchdog on target device  
        
        if (JTAGVERSION != JTAG_ID)
                return(STATUS_ERROR); 
        
        return(STATUS_OK);
}

//----------------------------------------------------------------------------
/* Function to take target device under JTAG control. Disables the target
   watchdog. Sets the global DEVICE variable as read from the target device.	
   Arguments: None
   Result:    word (STATUS_ERROR if fuse is blown, incorrect JTAG ID or
                    synchronizing time-out; STATUS_OK otherwise)
*/
word GetDevice(void)
{
  word i;
  
  DEVICE = 0;                           // Preset DEVICE with "not a device"
  ResetTAP();                           // Reset JTAG state machine, check fuse HW
   
  if (IsFuseBlown())                    // Stop here if fuse is already blown
    return(STATUS_ERROR);  

  IR_Shift(IR_CNTRL_SIG_16BIT);
  DR_Shift16(0x2401);                   // Set device into JTAG mode + read
  if (IR_Shift(IR_CNTRL_SIG_CAPTURE) != JTAG_ID)
    return(STATUS_ERROR);
  
  // Wait until CPU is synchronized, timeout after a limited # of attempts
  for (i = 50; i > 0; i--)
  {
        if ((DR_Shift16(0x0000) & 0x0200) == 0x0200)
        {
                DEVICE = ReadMem(F_WORD, 0x0FF0);	// Get target device type 
                                                        //(bytes are interchanged)
                DEVICE = (DEVICE << 8) + (DEVICE >> 8);	// Set global DEVICE type 
                break;
        }
        else if (i == 1)
            return(STATUS_ERROR);           // Timeout reached, return false
  }
  if (!ExecutePUC())                            // Perform PUC, Includes  
        return(STATUS_ERROR);                   // target Watchdog disable.

  return(STATUS_OK);
}

//----------------------------------------------------------------------------
/* Function to set target CPU JTAG FSM into the instruction fetch state
   Argument: None
   Result:   word (STATUS_OK if instr. fetch was set, STATUS_ERROR otherwise)
*/
word SetInstrFetch(void)
{
  word i;

  IR_Shift(IR_CNTRL_SIG_CAPTURE);
  
  // Wait until CPU is in instr. fetch state, timeout after limited attempts
  for (i = 50; i > 0; i--)
  {
    ClrTCLK();
    SetTCLK();
    if ((DR_Shift16(0x0000) & 0x0080) == 0x0080)
        return(STATUS_OK); 
  }
  return(STATUS_ERROR); 
}

//----------------------------------------------------------------------------
/* Load a given address into the target CPU's program counter (PC).
   Argument: word Addr (destination address)
   Result:   None
*/
void SetPC(word Addr)
{
  SetInstrFetch();              // Set CPU into instruction fetch mode, TCLK=1
  
  // Load PC with address
  IR_Shift(IR_CNTRL_SIG_16BIT);
  DR_Shift16(0x3401);           // CPU has control of RW & BYTE.
  IR_Shift(IR_DATA_16BIT);
  DR_Shift16(0x4030);           // "mov #addr,PC" instruction
  SetTCLK();
  ClrTCLK();
  DR_Shift16(Addr);             // Send addr value
  SetTCLK();
  ClrTCLK();
  SetTCLK();
  ClrTCLK();                    // Now the PC should be on Addr
  IR_Shift(IR_ADDR_CAPTURE);
  //~ if (Addr != DR_Shift16(0)) printf("ERROR: SetPC failed!\n");
  //~ IR_Shift(IR_CNTRL_SIG_16BIT);
  DR_Shift16(0x2401);           // JTAG has control of RW & BYTE.
}

//----------------------------------------------------------------------------
/* Function to set the CPU into a controlled stop state
*/
void HaltCPU(void)
{
  SetInstrFetch();              // Set CPU into instruction fetch mode
  
  ClrTCLK();                //lch
  IR_Shift(IR_CNTRL_SIG_16BIT);
  DR_Shift16(0x2401);
  IR_Shift(IR_DATA_16BIT);
  DR_Shift16(0x3FFF);           // Send JMP $ instruction
  SetTCLK();
  ClrTCLK();
  IR_Shift(IR_CNTRL_SIG_16BIT);
  DR_Shift16(0x2409);           // Set JTAG_HALT bit
  SetTCLK();
}

//----------------------------------------------------------------------------
/* Function to release the target CPU from the controlled stop state
*/
void ReleaseCPU(void)
{
  ClrTCLK();
  IR_Shift(IR_CNTRL_SIG_16BIT);
  DR_Shift16(0x2401);           // Clear the HALT_JTAG bit
  IR_Shift(IR_ADDR_CAPTURE);
  SetTCLK();
}

//----------------------------------------------------------------------------
/* Function to release the target device from JTAG control
   Argument: word Addr (0xFFFE: Perform Reset, means Load Reset Vector into PC,
                        otherwise: Load Addr into PC)
   Result:   None
*/
void ReleaseDevice(word Addr)
{
  if (Addr == V_RESET)
  {
    IR_Shift(IR_CNTRL_SIG_16BIT);
    DR_Shift16(0x2C01);         // Perform a reset
    DR_Shift16(0x2401);
  }
  else
    SetPC(Addr);                // Set target CPU's PC
  IR_Shift(IR_CNTRL_SIG_RELEASE);
}

//----------------------------------------------------------------------------
/* This function compares the computed PSA (Pseudo Signature Analysis) value
   to the PSA value shifted out from the target device.
   It is used for very fast data block write or erasure verification.
   Arguments: word StartAddr (Start address of data block to be checked)
              word Length (Number of words within data block)
              word *DataArray (Pointer to array with the data, 0 for Erase Check)
   Result:    word (STATUS_OK if comparison was successful, STATUS_ERROR otherwise)
*/
word VerifyPSA(word StartAddr, word Length, word *DataArray)
{
  word TDOword, i;
  word POLY = 0x0805;           // Polynom value for PSA calculation
  word PSA_CRC = StartAddr-2;   // Start value for PSA calculation

  ExecutePUC();          
  IR_Shift(IR_CNTRL_SIG_16BIT);
  DR_Shift16(0x2401);
  SetInstrFetch();
  IR_Shift(IR_DATA_16BIT);
  DR_Shift16(0x4030);
  SetTCLK();
  ClrTCLK();
  DR_Shift16(StartAddr-2);
  SetTCLK();
  ClrTCLK();
  SetTCLK();
  ClrTCLK();
  SetTCLK();
  ClrTCLK();
  IR_Shift(IR_ADDR_CAPTURE);
  DR_Shift16(0x0000);
  IR_Shift(IR_DATA_PSA);
  for (i = 0; i < Length; i++)
  {
  // Calculate the PSA (Pseudo Signature Analysis) value  
    if ((PSA_CRC & 0x8000) == 0x8000)
    {
      PSA_CRC ^= POLY;
      PSA_CRC <<= 1;
      PSA_CRC |= 0x0001;
    }
    else
    {
      PSA_CRC <<= 1;
    }
    // if pointer is 0 then use erase check mask, otherwise data  
    &DataArray[0] == 0 ? (PSA_CRC ^= 0xFFFF) : (PSA_CRC ^= DataArray[i]);
    
    // Clock through the PSA  
    SetTCLK();
    ClrTCK();
    SetTMS();
    SetTCK();                 // Select DR scan
    ClrTCK();
    ClrTMS();
    SetTCK();                 // Capture DR
    ClrTCK();
    SetTCK();                 // Shift DR
    ClrTCK();
    SetTMS();
    SetTCK();                 // Exit DR
    ClrTCK();
    SetTCK();
    ClrTMS();
    ClrTCK();
    SetTCK();
    ClrTCLK();
  }
  IR_Shift(IR_SHIFT_OUT_PSA);
  TDOword = DR_Shift16(0x0000);   // Read out the PSA value
  SetTCLK();
  
  return((TDOword == PSA_CRC) ? STATUS_OK : STATUS_ERROR);
}  

//----------------------------------------------------------------------------
/* This function writes one byte/word at a given address ( <0xA00) 
   Arguments: word Format (F_BYTE or F_WORD)
              word Addr (Address of data to be written)
              word Data (shifted data)  
   Result:    None
*/
void WriteMem(word Format, word Addr, word Data)
{
  HaltCPU();
  
  ClrTCLK();
  IR_Shift(IR_CNTRL_SIG_16BIT);
  if  (Format == F_WORD)
        DR_Shift16(0x2408);     // Set word write
  else
        DR_Shift16(0x2418);     // Set byte write
  IR_Shift(IR_ADDR_16BIT);
  DR_Shift16(Addr);             // Set addr
  IR_Shift(IR_DATA_TO_ADDR);
  DR_Shift16(Data);             // Shift in 16 bits
  SetTCLK();

  ReleaseCPU();
}

//----------------------------------------------------------------------------
/* This function writes an array of words into teh target memory.
   Arguments: word StartAddr (Start address of target memory)
              word Length (Number of words to be programmed)
              word *DataArray (Pointer to array with the data)
   Result:    None
*/
void WriteMemQuick(word StartAddr, word Length, word *DataArray)
{
  word i;
  
  // Initialize writing:
  SetPC((word)(StartAddr-4));
  HaltCPU();
  
  ClrTCLK();
  IR_Shift(IR_CNTRL_SIG_16BIT);
  DR_Shift16(0x2408);           // Set RW to write
  IR_Shift(IR_DATA_QUICK);
  for (i = 0; i < Length; i++)
  {
    DR_Shift16(DataArray[i]);   // Shift in the write data
    SetTCLK();
    ClrTCLK();                  // Increment PC by 2
  }
  SetTCLK();
  
  ReleaseCPU();
}

//----------------------------------------------------------------------------
/* This function reads one byte/word from a given address in memory
   Arguments: word Format (F_BYTE or F_WORD)
              word Addr (address of memory)
   Result:    word (content of the addressed memory location)
*/
word ReadMem(word Format, word Addr)
{
  word TDOword;
  
  HaltCPU();
  
  ClrTCLK();
  IR_Shift(IR_CNTRL_SIG_16BIT);
  if  (Format == F_WORD)
        DR_Shift16(0x2409);     // Set word read
  else
        DR_Shift16(0x2419);     // Set byte read
  IR_Shift(IR_ADDR_16BIT);
  DR_Shift16(Addr);             // Set address
  IR_Shift(IR_DATA_TO_ADDR);
  SetTCLK();
  
  ClrTCLK();
  TDOword = DR_Shift16(0x0000);	// Shift out 16 bits
  SetTCLK();

  ReleaseCPU();
  return(Format == F_WORD ? TDOword : TDOword & 0x00FF);
}

//----------------------------------------------------------------------------
/* This function reads an array of words from a memory.
   Arguments: word StartAddr (Start address of memory to be read)
              word Length (Number of words to be read)
              word *DataArray (Pointer to array for the data)
   Result:    None
*/
void ReadMemQuick(word StartAddr, word Length, word *DataArray)
{
  word i;
  
  // Initialize reading:
  SetPC(StartAddr-4);
  HaltCPU();
  
  ClrTCLK();
  IR_Shift(IR_CNTRL_SIG_16BIT);
  DR_Shift16(0x2409);                   // Set RW to read
  IR_Shift(IR_DATA_QUICK);
  
  for (i = 0; i < Length; i++)
  {
    SetTCLK();
    ClrTCLK();
    DataArray[i] = DR_Shift16(0x0000); // Shift out the data
                                       // from the target.
  }
  SetTCLK();
  
  ReleaseCPU();
}

//----------------------------------------------------------------------------
/* This function performs a mass erase (with and w/o info memory) or a segment
   erase of a FLASH module specified by the given mode and address.
   Large memory devices get additional mass erase operations to meet the spec.
   Arguments: word Mode (could be ERASE_MASS or ERASE_MAIN or ERASE_SGMT)
              word Addr (any address within the selected segment)
   Result:    None
   Remark:    Could be extended with erase check via PSA.
*/
void EraseFLASH(word EraseMode, word EraseAddr)
{
  word StrobeAmount = 4820;             // default for Segment Erase  
  word i, loopcount = 1;                // erase cycle repeating for Mass Erase
  
  if ((EraseMode == ERASE_MASS) || (EraseMode == ERASE_MAIN))
  {  
        StrobeAmount = 5300;            // Larger Flash memories require
        loopcount = 19;                 // additional cycles for erase.
  }
  
  for (i = loopcount; i > 0; i--)
  {
    HaltCPU();
    
    ClrTCLK();
    IR_Shift(IR_CNTRL_SIG_16BIT);
    DR_Shift16(0x2408);                 // set RW to write
    IR_Shift(IR_ADDR_16BIT);
    DR_Shift16(0x0128);                 // FCTL1 address
    IR_Shift(IR_DATA_TO_ADDR);
    DR_Shift16(EraseMode);              // Enable erase mode
    SetTCLK();
    
    ClrTCLK();
    IR_Shift(IR_ADDR_16BIT);
    DR_Shift16(0x012A);                 // FCTL2 address
    IR_Shift(IR_DATA_TO_ADDR);
    DR_Shift16(0xA540);                 // MCLK is source, DIV=1
    SetTCLK();
    
    ClrTCLK();
    IR_Shift(IR_ADDR_16BIT);
    DR_Shift16(0x012C);                 // FCTL3 address
    IR_Shift(IR_DATA_TO_ADDR);
    DR_Shift16(0xA500);                 // Clear FCTL3
    SetTCLK();
    
    ClrTCLK();
    IR_Shift(IR_ADDR_16BIT);
    DR_Shift16(EraseAddr);              // Set erase address
    IR_Shift(IR_DATA_TO_ADDR);
    DR_Shift16(0x55AA);                 // Dummy write to start erase
    SetTCLK();
    
    ClrTCLK();
    IR_Shift(IR_CNTRL_SIG_16BIT);
    DR_Shift16(0x2409);                 // Set RW to read
    TCLKstrobes(StrobeAmount);          // Provide TCLKs
    IR_Shift(IR_CNTRL_SIG_16BIT);
    DR_Shift16(0x2408);                 // Set RW to write
    IR_Shift(IR_ADDR_16BIT);
    DR_Shift16(0x0128);                 // FCTL1 address
    IR_Shift(IR_DATA_TO_ADDR);
    DR_Shift16(0xA500);                 // Disable erase
    SetTCLK();

    ReleaseCPU();
  }
}

//----------------------------------------------------------------------------
/* This function performs an Erase Check over the given memory range
   Arguments: word StartAddr (Start address of memory to be checked)
              word Length (Number of words to be checked)
   Result:    word (STATUS_OK if erase check was successful, STATUS_ERROR otherwise)
*/
word EraseCheck(word StartAddr, word Length)
{
  return (VerifyPSA(StartAddr, Length, 0));
}

//----------------------------------------------------------------------------
/* This function performs a Verification over the given memory range
   Arguments: word StartAddr (Start address of memory to be verified)
              word Length (Number of words to be verified)
              word *DataArray (Pointer to array with the data)
   Result:    word (STATUS_OK if verification was successful, STATUS_ERROR otherwise)
*/
word VerifyMem(word StartAddr, word Length, word *DataArray)
{
  return (VerifyPSA(StartAddr, Length, &DataArray[0]));
}

//----------------------------------------------------------------------------
/* This function programs/verifies an array of words into an FLASH by
   using the FLASH controller. The JTAG FLASH register isn't needed.
   Arguments: word StartAddr (Start address of FLASH memory)
              word Length (Number of words to be programmed)
              word *DataArray (Pointer to array with the data)
   Result:    None
*/
void WriteFLASH(word StartAddr, word Length, word *DataArray)
{
  word i;                       // Loop counter
  word addr = StartAddr;        // Address counter
  
  HaltCPU();
  
  ClrTCLK();
  IR_Shift(IR_CNTRL_SIG_16BIT);
  DR_Shift16(0x2408);           // Set RW to write
  IR_Shift(IR_ADDR_16BIT);
  DR_Shift16(0x0128);           // FCTL1 register
  IR_Shift(IR_DATA_TO_ADDR);
  DR_Shift16(0xA540);           // Enable FLASH write
  SetTCLK();
  
  ClrTCLK();
  IR_Shift(IR_ADDR_16BIT);
  DR_Shift16(0x012A);           // FCTL2 register
  IR_Shift(IR_DATA_TO_ADDR);
  DR_Shift16(0xA540);           // Select MCLK as source, DIV=1
  SetTCLK();
  
  ClrTCLK();
  IR_Shift(IR_ADDR_16BIT);
  DR_Shift16(0x012C);           // FCTL3 register
  IR_Shift(IR_DATA_TO_ADDR);
  DR_Shift16(0xA500);           // Clear FCTL3 register
  SetTCLK();
  
  ClrTCLK();
  for (i = 0; i < Length; i++, addr += 2)
  {
    IR_Shift(IR_CNTRL_SIG_16BIT);
    DR_Shift16(0x2408);         // Set RW to write
    IR_Shift(IR_ADDR_16BIT);
    DR_Shift16(addr);           // Set address
    IR_Shift(IR_DATA_TO_ADDR);
    DR_Shift16(DataArray[i]);	// Set data
    SetTCLK();
    ClrTCLK();
        IR_Shift(IR_CNTRL_SIG_16BIT);
    DR_Shift16(0x2409);         // Set RW to read
        TCLKstrobes(35);        // Provide TCLKs, min. 33 for F149 and F449 
  }
  IR_Shift(IR_CNTRL_SIG_16BIT);
  DR_Shift16(0x2408);           // Set RW to write
  IR_Shift(IR_ADDR_16BIT);
  DR_Shift16(0x0128);           // FCTL1 register
  IR_Shift(IR_DATA_TO_ADDR);
  DR_Shift16(0xA500);           // Disable FLASH write
  SetTCLK();

  ReleaseCPU();
}

//----------------------------------------------------------------------------
/* This function programs/verifies a set of data arrays of words into a FLASH
   memory by using the "WriteFLASH()" function. It conforms with the
   "CodeArray" structure convention of file "Target_Code.s43".
   Arguments: word *DataArray (Pointer to array with the data)
   Result:    word (STATUS_OK if verification was successful,
                    STATUS_ERROR otherwise)
*/
word WriteFLASHallSections(word *CodeArray)
{
  word s;                       // Number of sections
  word p;                       // Pointer to data
  
  for (s = CodeArray[0], p = 1; s > 0; s--)
  {
    // Write/Verify(PSA) one FLASH section
    WriteFLASH(CodeArray[p], CodeArray[p+1], &CodeArray[p+2]);
    if (!VerifyMem(CodeArray[p], CodeArray[p+1], &CodeArray[p+2]))
      return(STATUS_ERROR);
    // pointer of next section = old pointer + 2 + length of actual section      
    p += CodeArray[p+1] + 2;
  }
  return(STATUS_OK);
}    

//------------------------------------------------------------------------
/* This function checks if the JTAG access security fuse is blown.
   Arguments: None
   Result:    word (STATUS_OK if fuse is blown, STATUS_ERROR otherwise)
*/
word IsFuseBlown(void)
{
  word i;
  
  for (i = 3; i > 0; i--)               //  First trial could be wrong
  {
        IR_Shift(IR_CNTRL_SIG_CAPTURE);
        if (DR_Shift16(0xAAAA) == 0x5555)
            return(STATUS_OK);          // Fuse is blown
  }   
  return(STATUS_ERROR);                 // fuse is not blown
}

//------------------------------------------------------------------------
/* This function blows the security fuse.
   Arguments: None
   Result:    word (STATUS_OK if burn was successful, STATUS_ERROR otherwise)
*/
word BlowFuse(void)
{
  word mode = VPP_ON_TEST;      // Devices with TEST pin: VPP to TEST
      
  if ((DEVICE == 0xF149) || (DEVICE == 0xF449) ||    // w/o TEST pin are:
      (DEVICE == 0xF413) || (DEVICE == 0xF169))	     // F149, F449, F413, F169
  { // Devices without TEST pin
    IR_Shift(IR_CNTRL_SIG_16BIT);       // TDO becomes TDI functionality
    DR_Shift16(0x7201);
    TDOisInput();
    mode = VPP_ON_TDI;                  // Enable VPP on TDI
  }
    
  IR_Shift(IR_PREPARE_BLOW);            // Initialize fuse blowing
  Delay(1);
  VPPon(mode);                          // Switch VPP onto selected pin
  Delay(5);
  IR_Shift(IR_EX_BLOW);                 // Execute fuse blowing
  Delay(1);
 
  // Switch off power to target and wait
  ReleaseTarget();                      // switch VPP and VCC target off
  Delay(200);
  
  // Check fuse: switch power on, simulate an initial JTAG entry
  InitTarget();                         // Supply and preset Target Board
  ResetTAP();                           // Check fuse HW, reset JTAG state machine
  
  return(IsFuseBlown());                // Return result of "is fuse blown?" 
}

/****************************************************************************/
/*                         END OF SOURCE FILE                               */
/****************************************************************************/
